kwigbo/GBA-Consolizer/Models/Woozle_Gameboy_Switch_Buttons.3mf

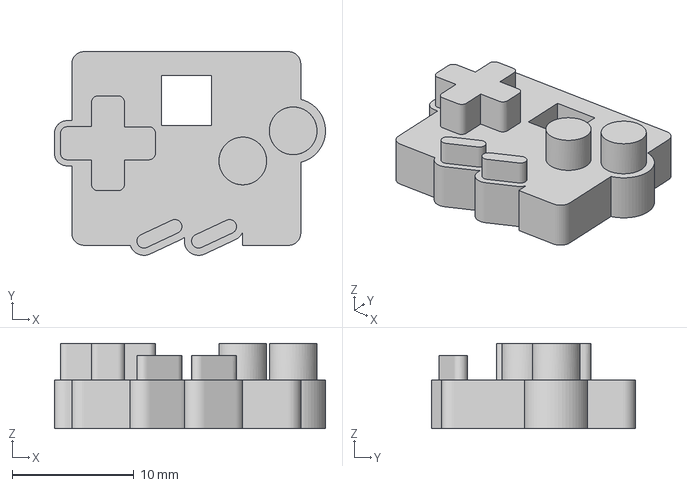
[picture p15: CAD file, 2022-08-18]
Models/Woozle_Gameboy_Switch_Buttons.3mf
22.2 x 16.7 x 7.00 mm
