kwigbo/GBA-Consolizer/Models/Rear_Plate_Bottom_Woozle.3mf

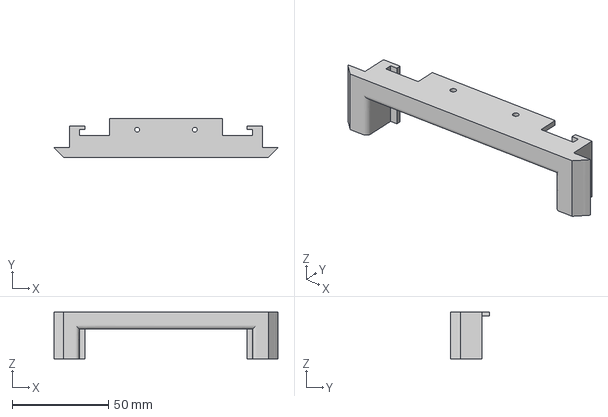
[picture p16: CAD file, 2022-08-18]
Models/Rear_Plate_Bottom_Woozle.3mf
116.3 x 20.0 x 24.2 mm
