kwigbo/GBA-Consolizer/Models/Face_Plate_Woozle.3mf

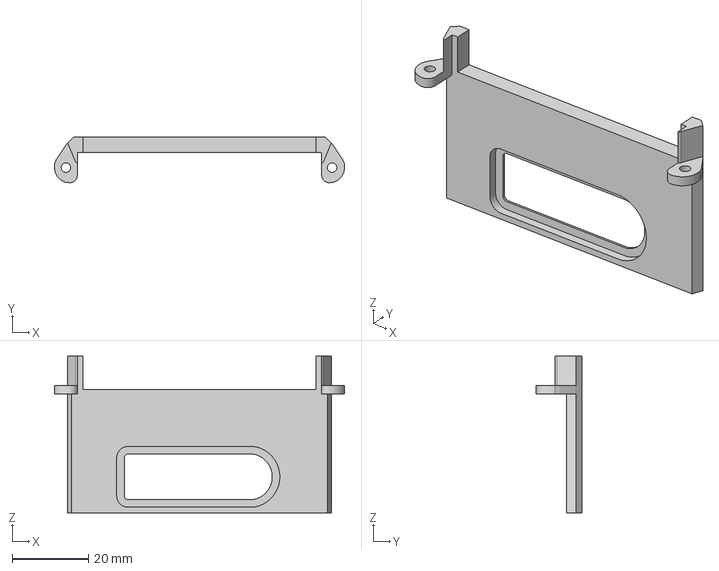
[picture p17: CAD file, 2022-08-18]
Models/Face_Plate_Woozle.3mf
76.2 x 12.0 x 41.2 mm
