kwigbo/GBA-Consolizer/Models/Support_Bar_Woozle.3mf

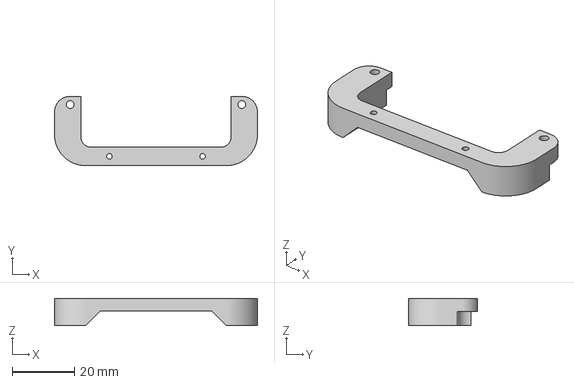
[picture p18: CAD file, 2022-08-17]
Models/Support_Bar_Woozle.3mf
65.4 x 22.3 x 8.75 mm
