kwigbo/GBA-Consolizer/Models/Lid_Type_3.3mf

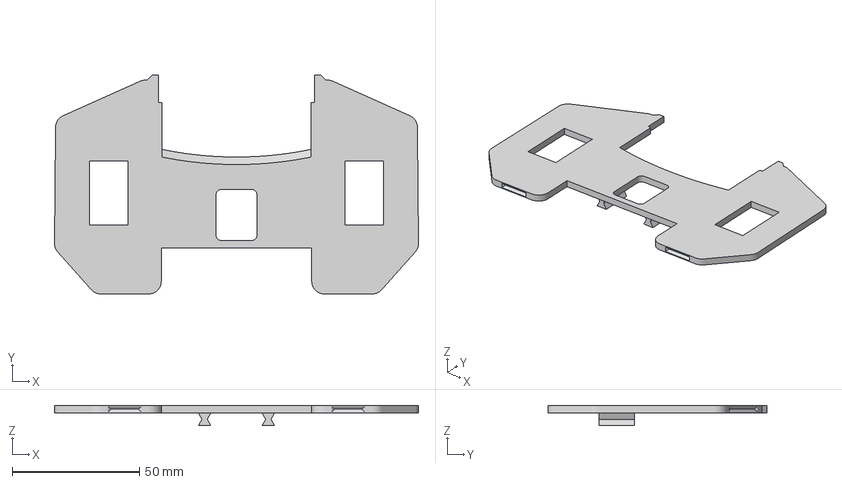
[picture p19: CAD file, 2022-08-08]
Models/Lid_Type_3.3mf
142.8 x 85.9 x 8.00 mm
