kwigbo/GBA-Consolizer/Models/Eject_Holder_Plate.3mf

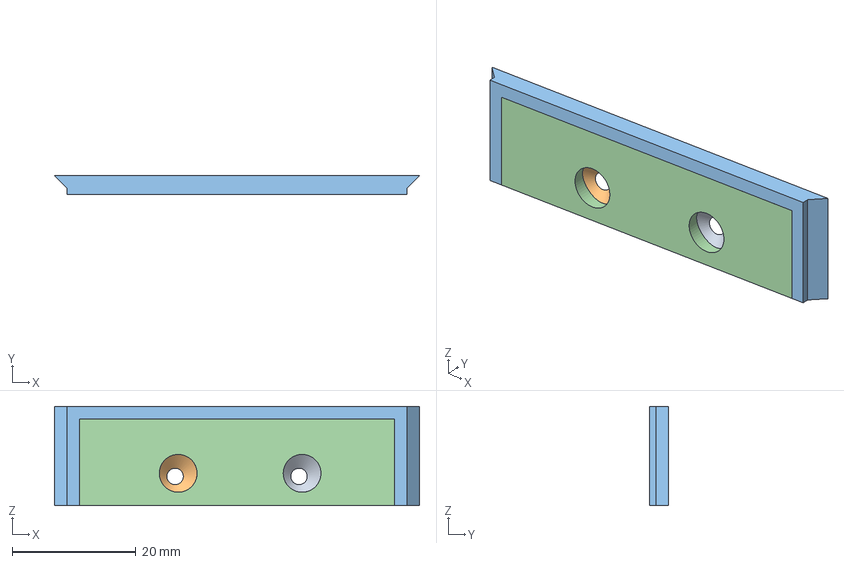
[picture p20: CAD file, 2022-07-26]
Models/Eject_Holder_Plate.3mf
58.9 x 3.00 x 16.0 mm
Hole 1
Hole 2
Plate Frame
Plate
