kwigbo/GBA-Consolizer/Models/Cartridge_Tray_Mount_40.3mf

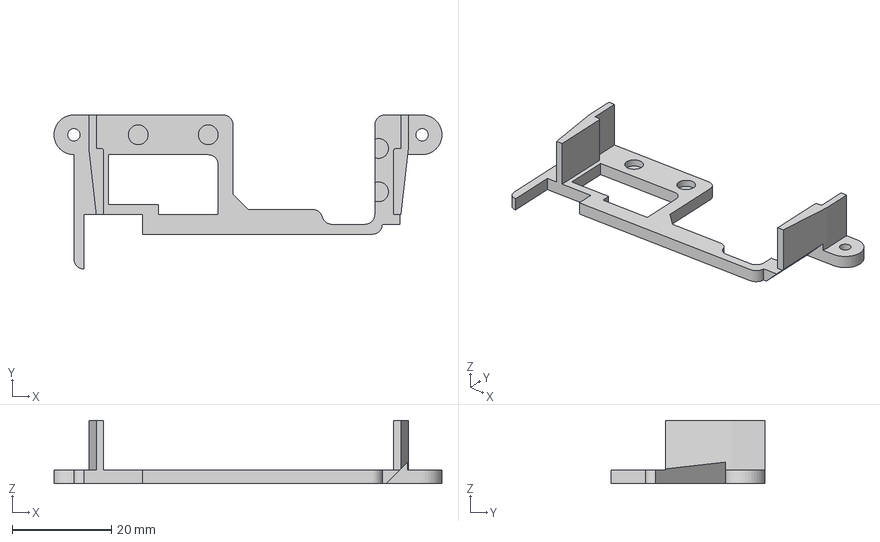
[picture p21: CAD file, 2022-07-25]
Models/Cartridge_Tray_Mount_40.3mf
78.0 x 31.0 x 12.8 mm
