kwigbo/GBA-Consolizer/Models/Cartridge_Tray_Base_40.3mf

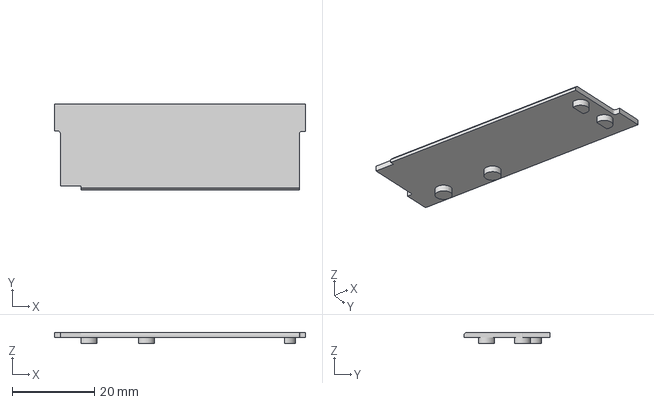
[picture p22: CAD file, 2022-07-25]
Models/Cartridge_Tray_Base_40.3mf
61.1 x 21.0 x 2.74 mm
