kwigbo/GBA-Consolizer/Models/Rear_Plate_Top.3mf

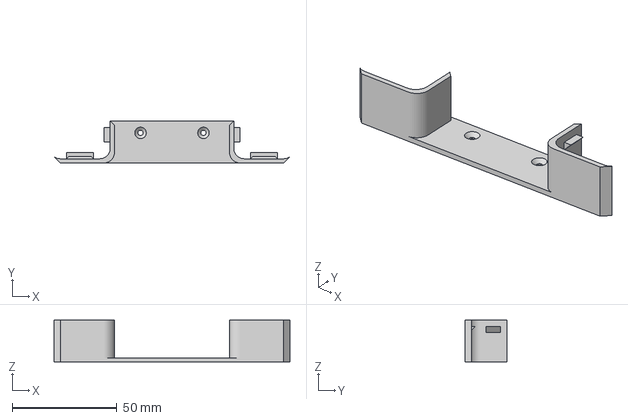
[picture p23: CAD file, 2022-07-25]
Models/Rear_Plate_Top.3mf
112.5 x 20.0 x 20.0 mm
