kwigbo/GBA-Consolizer/Models/Consolizer_Shell.3mf

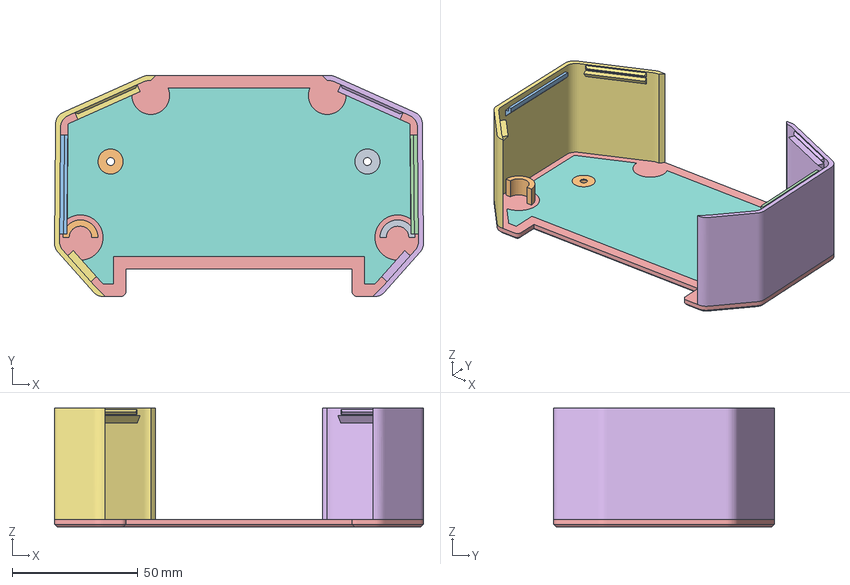
[picture p24: CAD file, 2022-07-23]
Models/Consolizer_Shell.3mf
146.9 x 88.0 x 47.2 mm
Catch 1
Catch 2
Catch Right
Catch left
Consolizer Shell Floor Edge
Consolizer Shell Left
Consolizer Shell Right
Floor Pattern
Screw Hole 1
Screw Hole 2
