kwigbo/GBA-Consolizer/Models/Cartridge_Tray_Mount_32.3mf

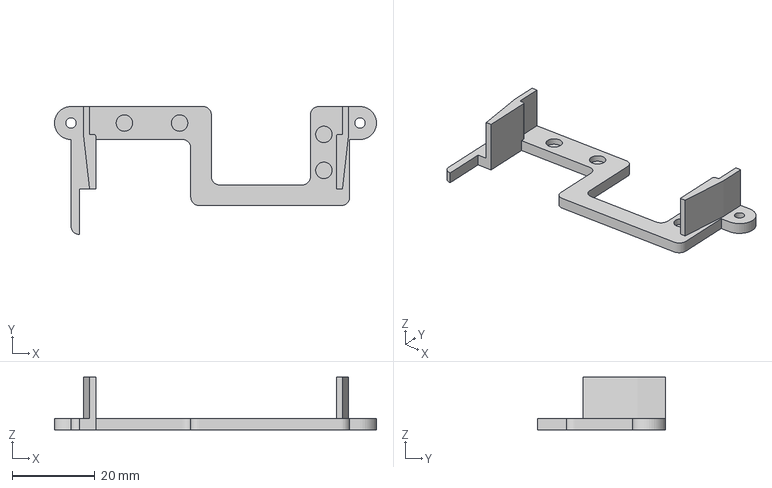
[picture p25: CAD file, 2022-07-23]
Models/Cartridge_Tray_Mount_32.3mf
78.0 x 31.0 x 12.8 mm
