kwigbo/GBA-Consolizer/Models/Board_Adapter_Left_Inserts_Gamebox.3mf

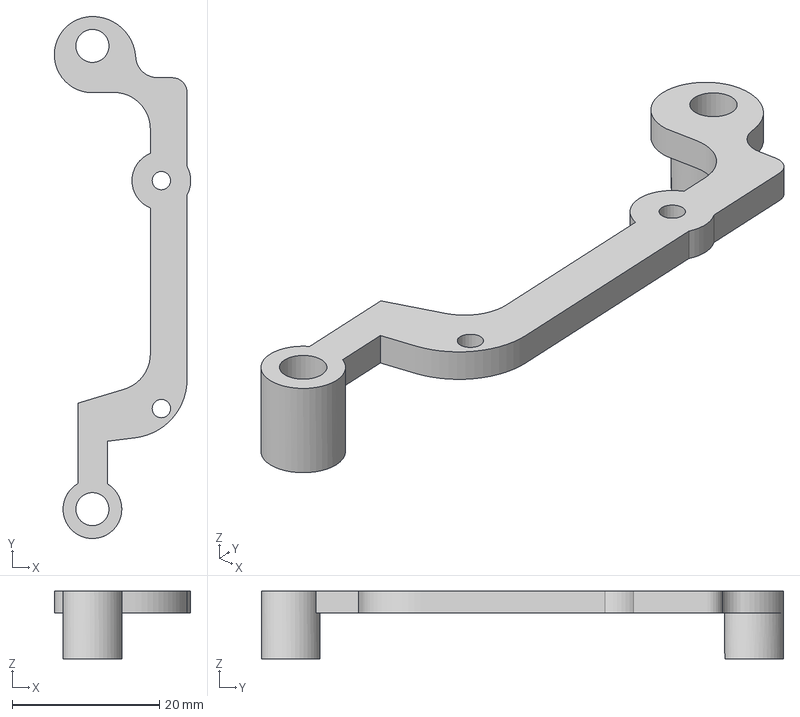
[picture p26: CAD file, 2022-07-19]
Models/Board_Adapter_Left_Inserts_Gamebox.3mf
18.6 x 71.0 x 9.20 mm
