kwigbo/GBA-Consolizer/Models/Consolizer_Mount_Right_Inserts.3mf

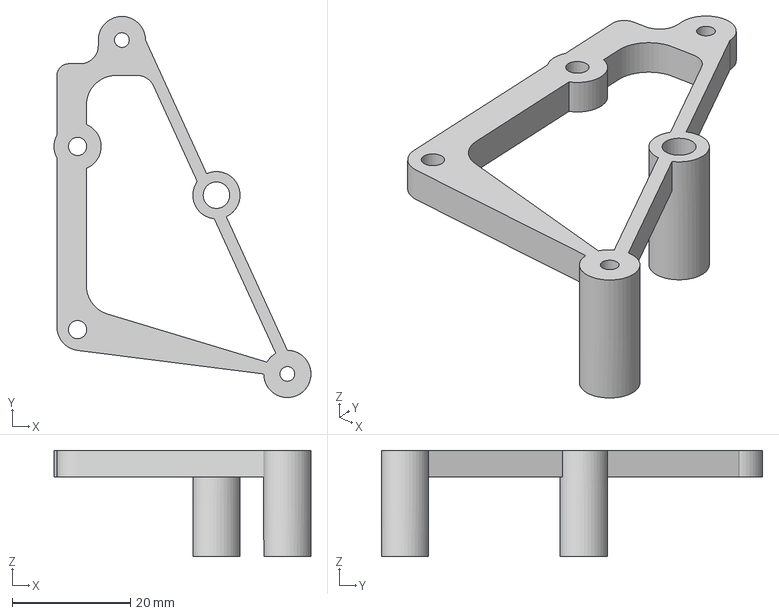
[picture p27: CAD file, 2022-07-19]
Models/Consolizer_Mount_Right_Inserts.3mf
43.5 x 64.5 x 18.0 mm
