kwigbo/GBA-Consolizer/Models/Rear_Plate_Bottom_Gamebox.3mf

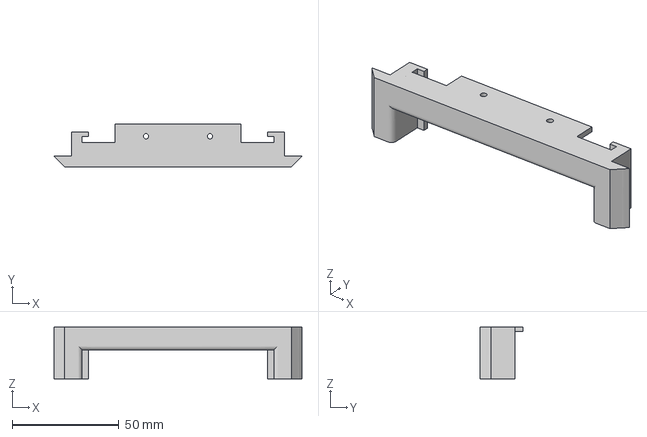
[picture p29: CAD file, 2022-07-19]
Models/Rear_Plate_Bottom_Gamebox.3mf
116.3 x 20.0 x 24.2 mm
