kwigbo/GBA-Consolizer/Models/Motherboard_Mount_Inserts.3mf

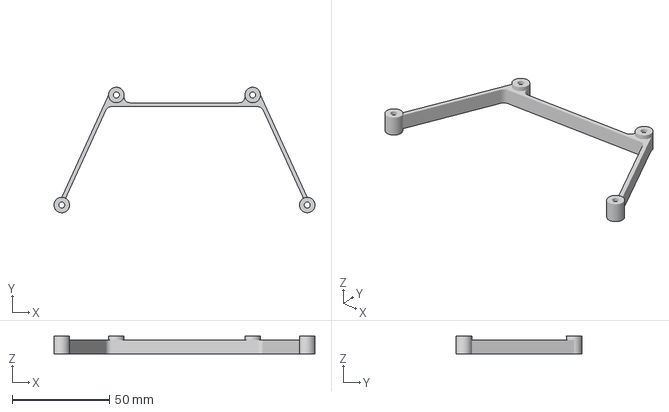
[picture p30: CAD file, 2022-07-19]
Models/Motherboard_Mount_Inserts.3mf
134.0 x 64.5 x 9.00 mm
