kwigbo/GBA-Consolizer/Models/Face_Plate_Button_Cap_Gamebox.3mf

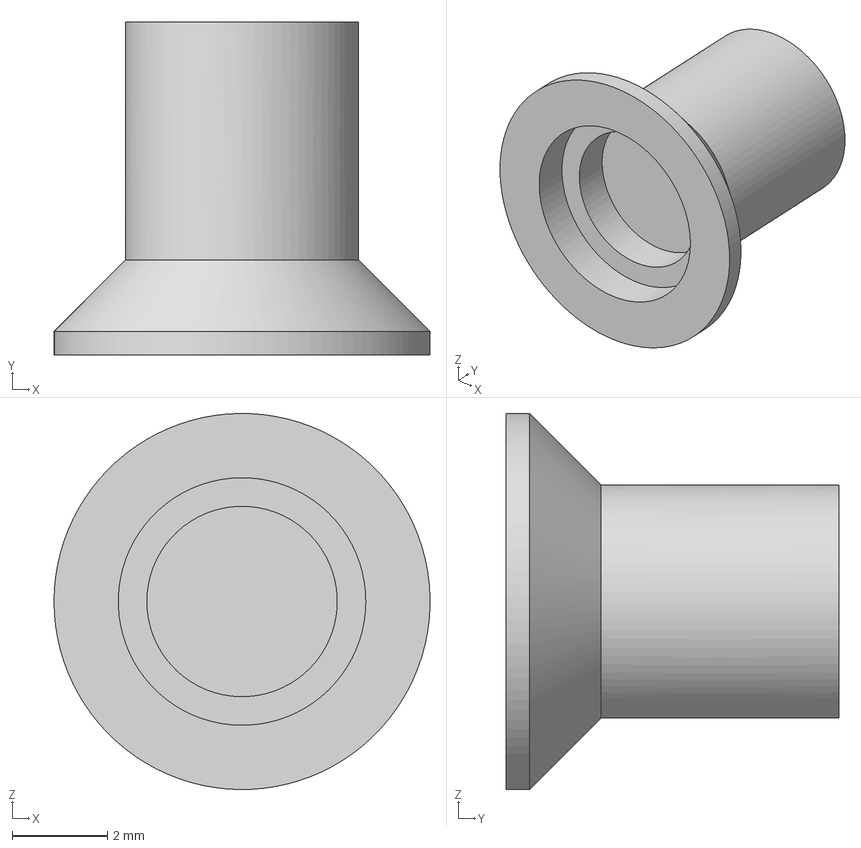
[picture p31: CAD file, 2022-07-19]
Models/Face_Plate_Button_Cap_Gamebox.3mf
7.90 x 7.00 x 7.90 mm
