kwigbo/GBA-Consolizer/Models/Motherboard_Mount.3mf

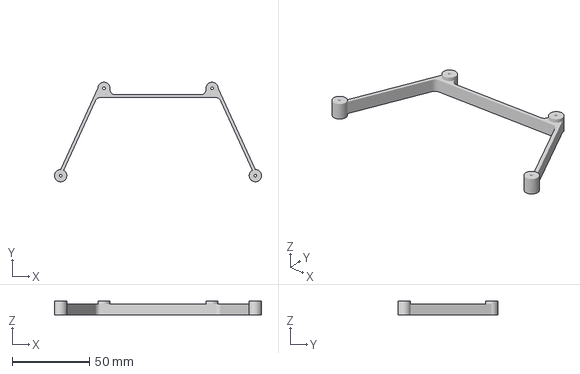
[picture p32: CAD file, 2022-07-19]
Models/Motherboard_Mount.3mf
134.0 x 64.5 x 9.00 mm
