kwigbo/GBA-Consolizer/Models/Rear_Portplate_Gamebox.3mf

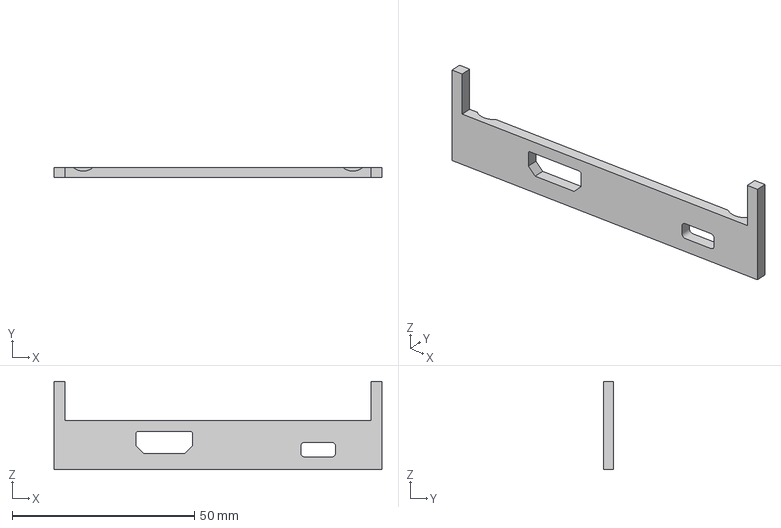
[picture p33: CAD file, 2022-07-19]
Models/Rear_Portplate_Gamebox.3mf
90.0 x 2.85 x 24.2 mm
