kwigbo/GBA-Consolizer/Models/Face_Plate_Gamebox.3mf

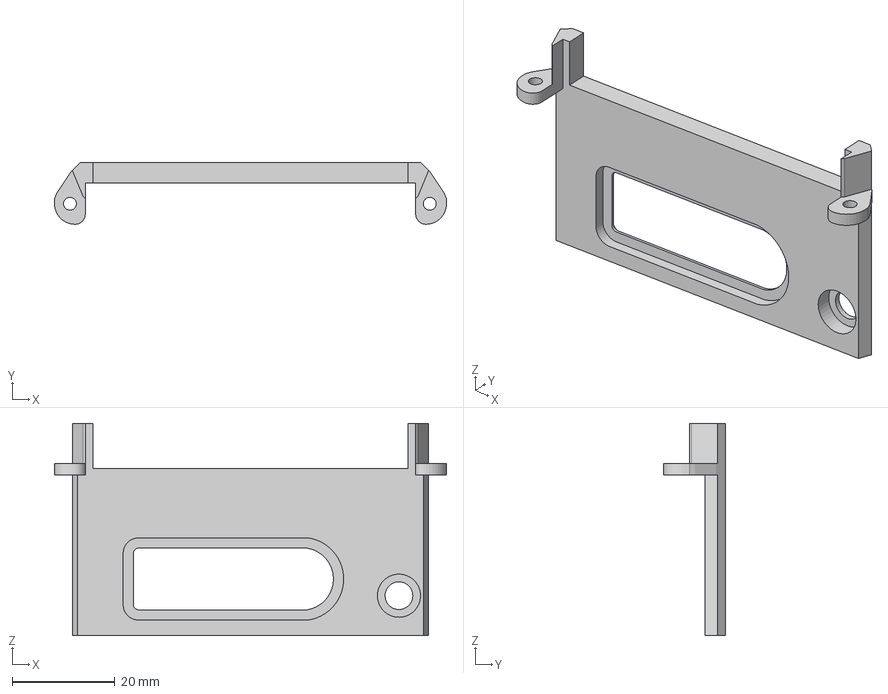
[picture p34: CAD file, 2022-07-19]
Models/Face_Plate_Gamebox.3mf
76.2 x 12.0 x 41.2 mm
