kwigbo/GBA-Consolizer/Models/Support_Bar_Gamebox.3mf

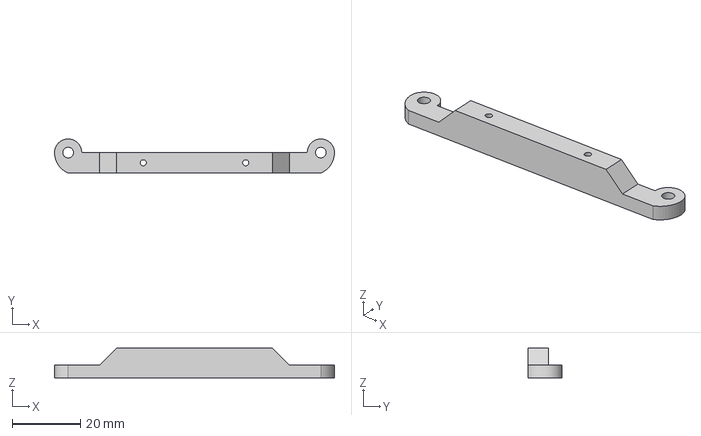
[picture p35: CAD file, 2022-07-19]
Models/Support_Bar_Gamebox.3mf
82.0 x 10.0 x 8.75 mm
