kwigbo/GBA-Consolizer/Models/Calibration_Top_Block.3mf

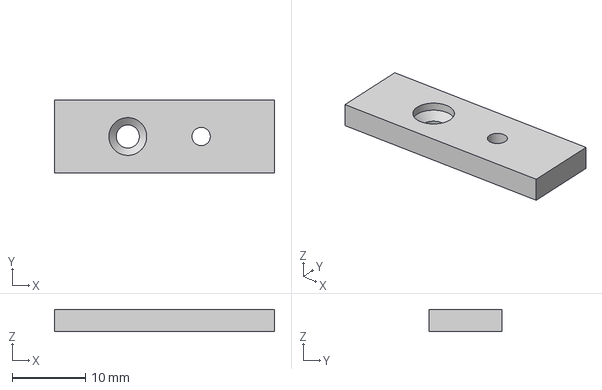
[picture p36: CAD file, 2022-07-19]
Models/Calibration_Top_Block.3mf
30.0 x 10.0 x 3.00 mm
