kwigbo/GBA-Consolizer/Models/Eject_Holder.3mf

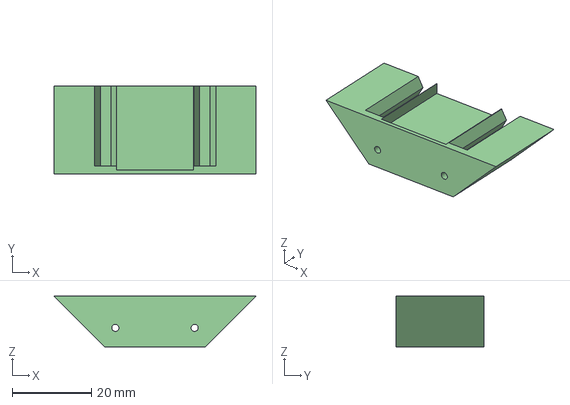
[picture p38: CAD file, 2022-07-19]
Models/Eject_Holder.3mf
50.9 x 22.2 x 12.8 mm
