kwigbo/GBA-Consolizer/Models/Eject_Holder_Inserts.3mf

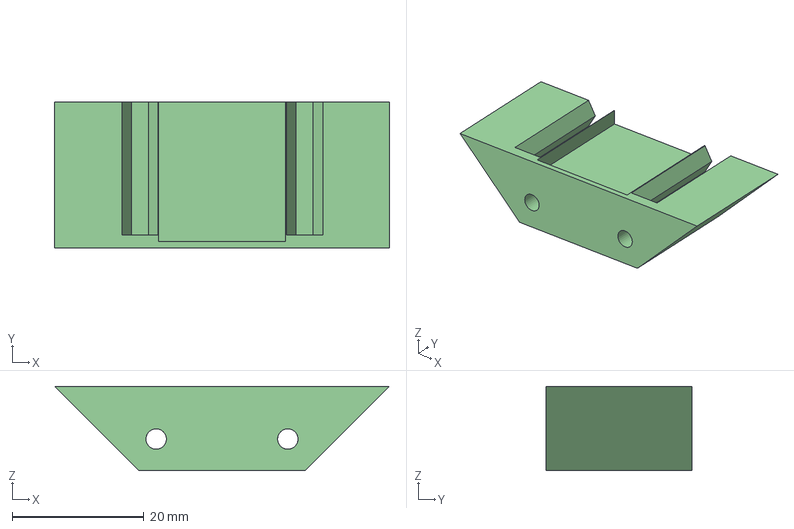
[picture p39: CAD file, 2022-07-19]
Models/Eject_Holder_Inserts.3mf
50.9 x 22.2 x 12.8 mm
