kwigbo/GBA-Consolizer/Models/Calibration_Bottom_Block_Inserts.3mf

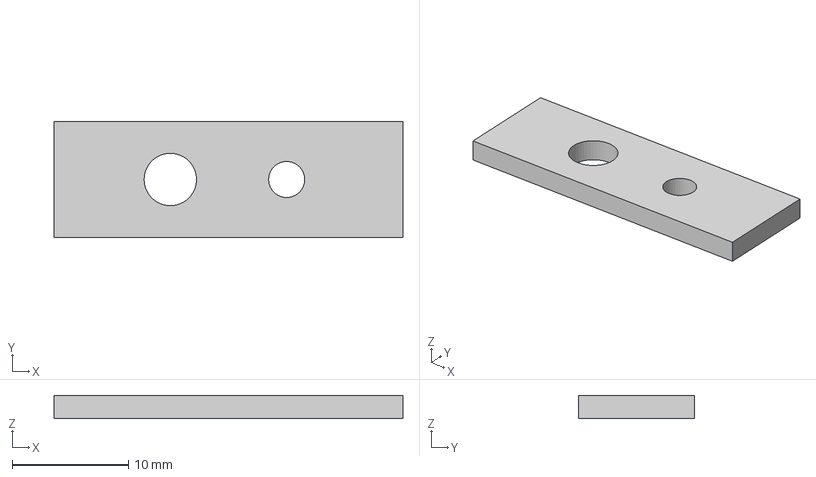
[picture p40: CAD file, 2022-07-19]
Models/Calibration_Bottom_Block_Inserts.3mf
30.0 x 10.0 x 2.00 mm
