kwigbo/GBA-Consolizer/Models/Eject_Switch.3mf

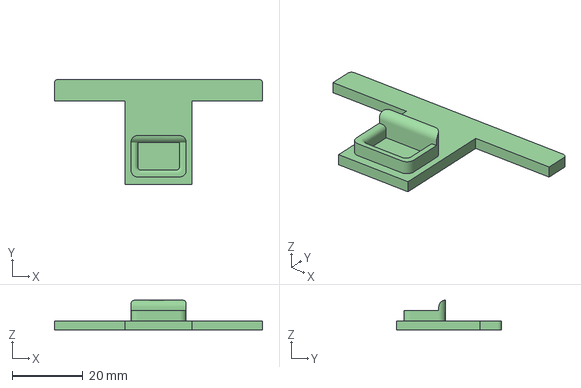
[picture p41: CAD file, 2022-07-19]
Models/Eject_Switch.3mf
58.9 x 29.8 x 8.45 mm
